madalinapal/InkTime/images/smartwatch_side_view2.png

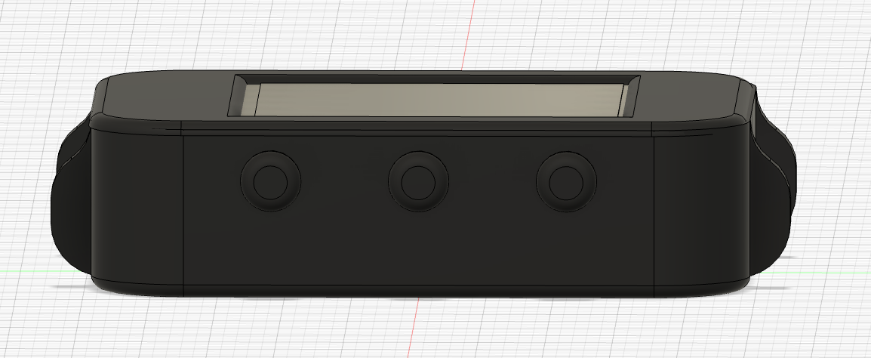
images/smartwatch_side_view2.png
